RichardKroesen/M33-Sound-Locator/analysis/insights/24125-geometric_accuracy_plot.png

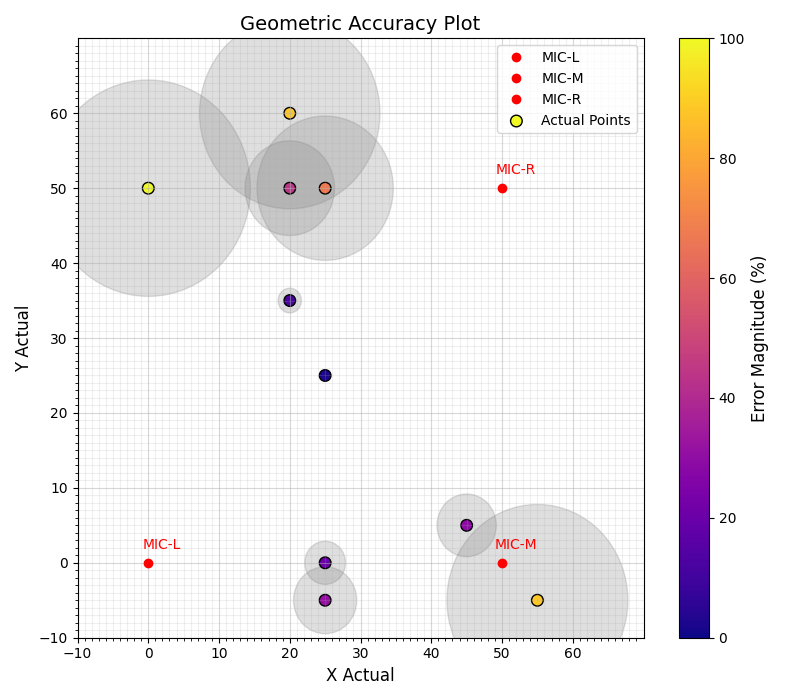
analysis/insights/24125-geometric_accuracy_plot.png
