RichardKroesen/M33-Sound-Locator/analysis/insights/AfterHW-LPF.png

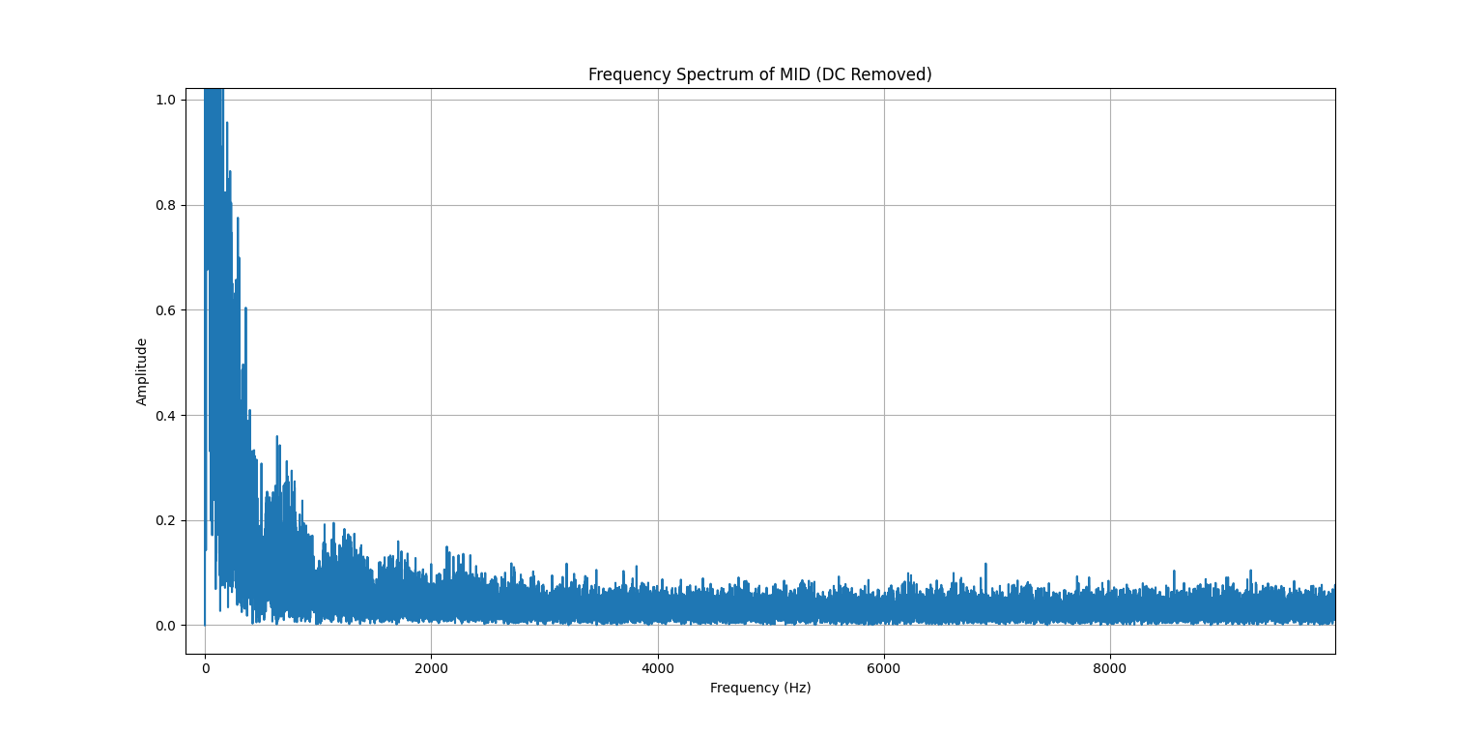
analysis/insights/AfterHW-LPF.png
