RichardKroesen/M33-Sound-Locator/analysis/insights/SW_FIR_signal_optimal_fcent4k-BW5-tps51.png

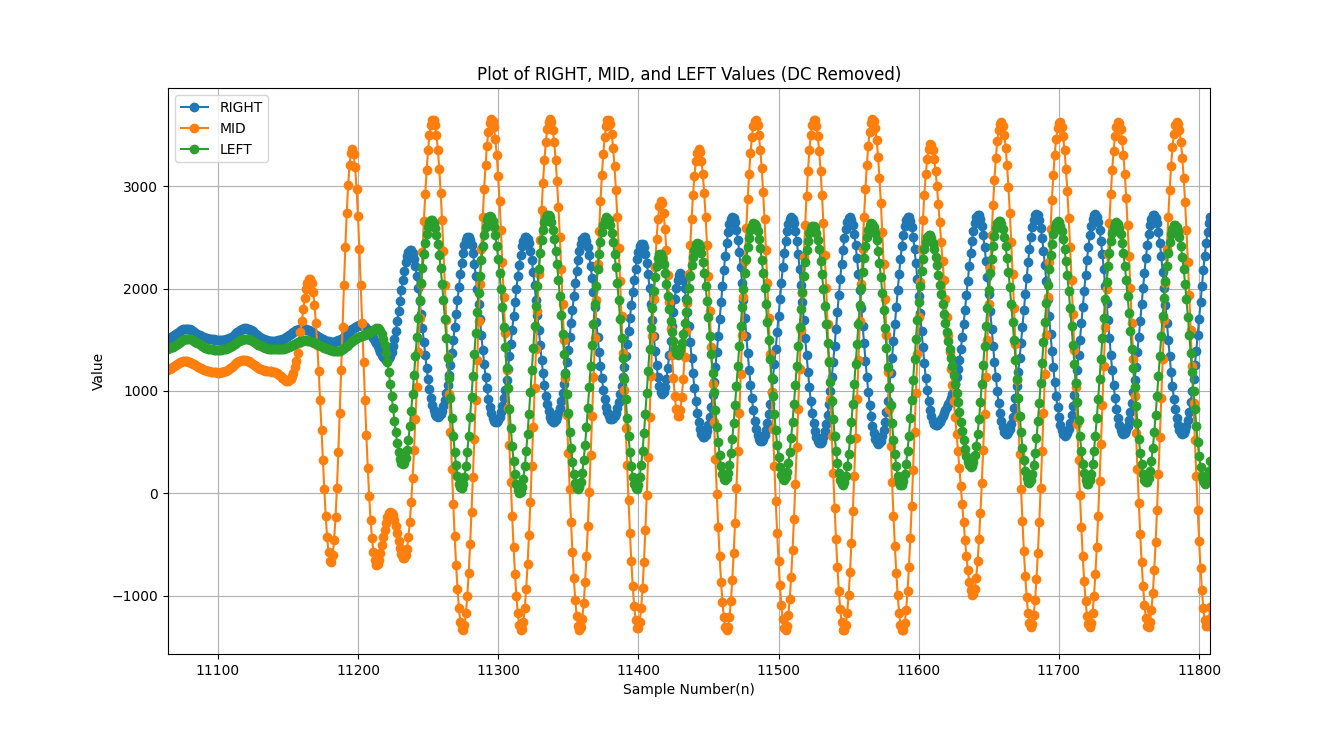
analysis/insights/SW_FIR_signal_optimal_fcent4k-BW5-tps51.png
