RichardKroesen/M33-Sound-Locator/electrical-mechnical-rsc/microphone-holder_sideview2.jpg

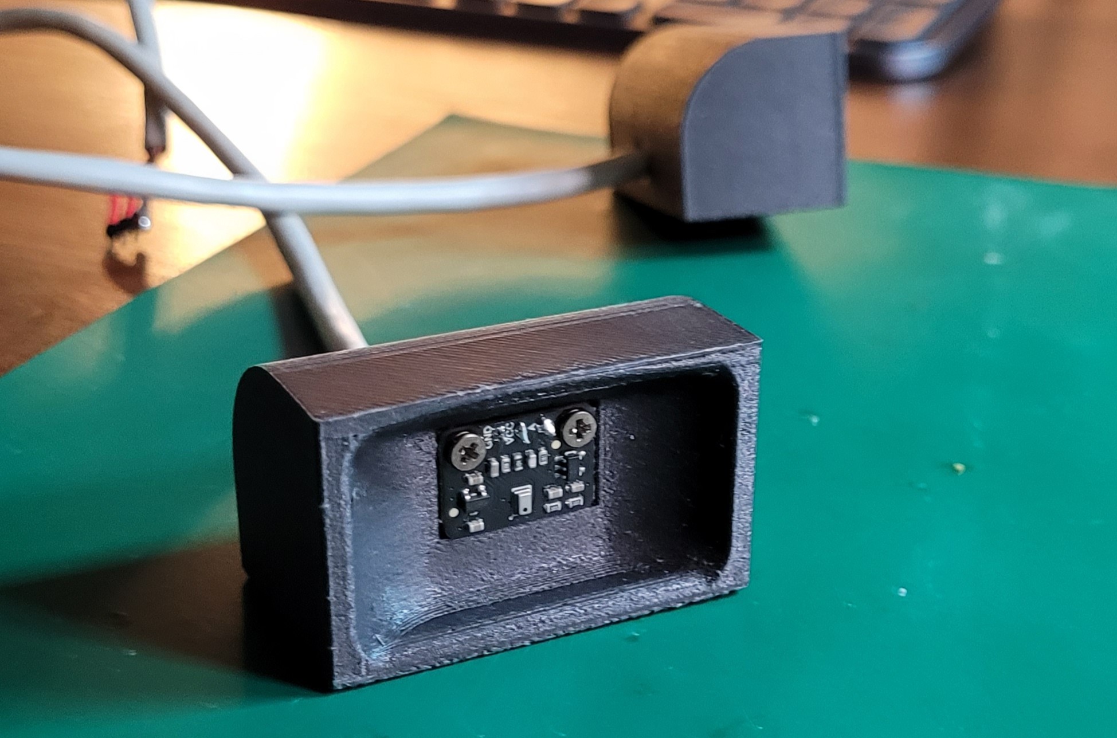
electrical-mechnical-rsc/microphone-holder_sideview2.jpg
