RichardKroesen/M33-Sound-Locator/electrical-mechnical-rsc/microphone_amplifier/perf-board_bottomview.jpg

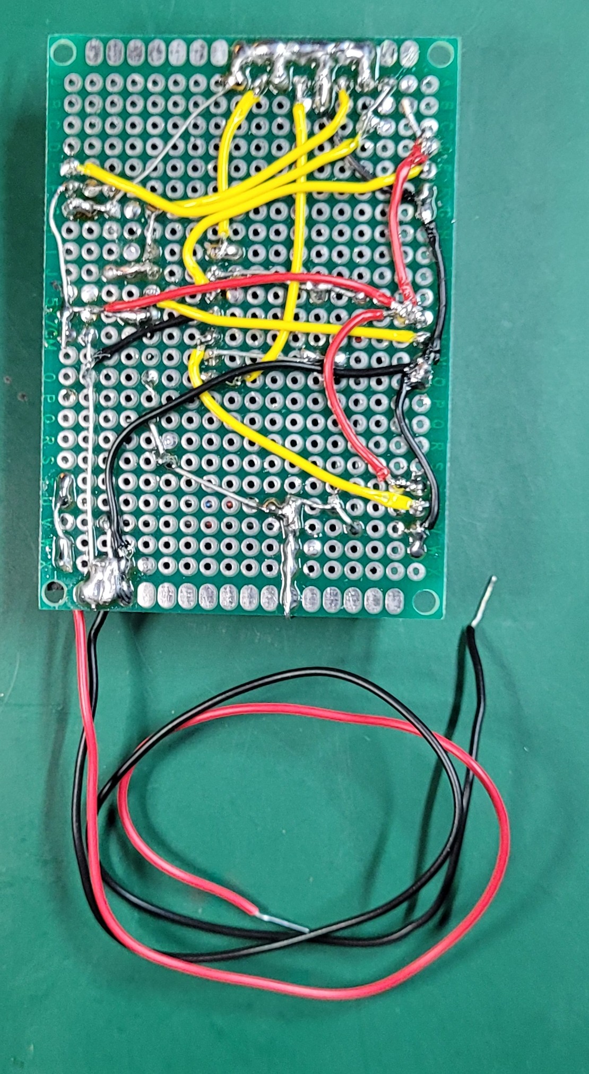
electrical-mechnical-rsc/microphone_amplifier/perf-board_bottomview.jpg
