RichardKroesen/M33-Sound-Locator/electrical-mechnical-rsc/microphone_amplifier/perf-board_topview.jpg

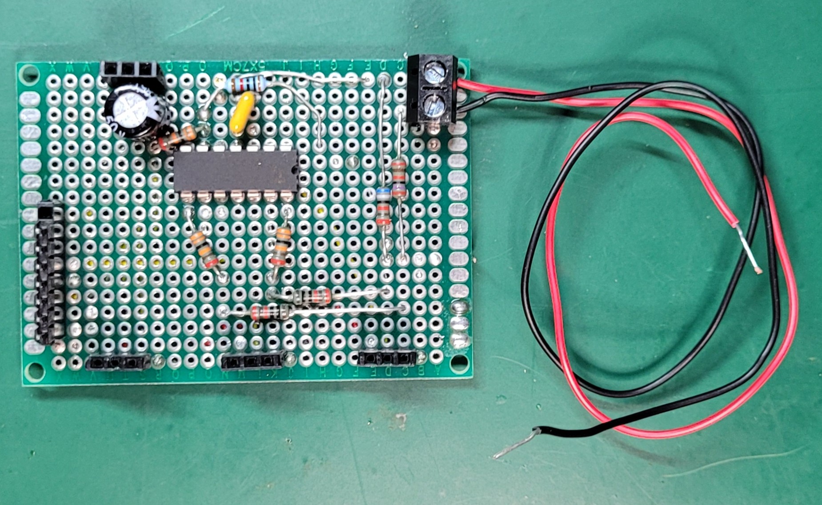
electrical-mechnical-rsc/microphone_amplifier/perf-board_topview.jpg
