RichardKroesen/M33-Sound-Locator/electrical-mechnical-rsc/Complete_hardware_setup_overview.jpg

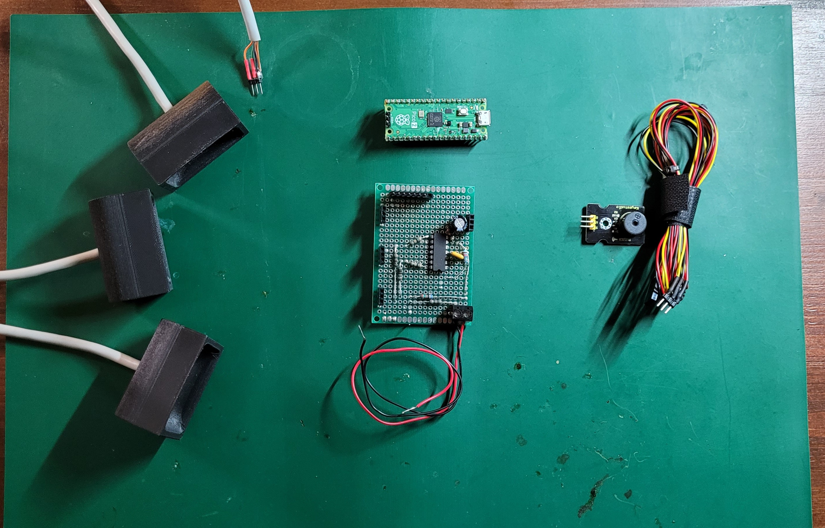
electrical-mechnical-rsc/Complete_hardware_setup_overview.jpg
