RichardKroesen/M33-Sound-Locator/models/Amplifier/AmplifierModel.asc

R1: res; 15k
R2: res; 200k
R3: res; 1
R4: res; 68k
R5: res; 27k
U1: LT1413
V1: voltage; 5
V2: voltage; SINE(1.5 0.15 1)
V3: voltage; 0
V4: voltage; 5
Named nets: 0, OutputSig
.tran 10
