RichardKroesen/M33-Sound-Locator/src/main.hpp

/** MIT License
 * 
 * Copyright (c) 2025 Feb. by Julian Bruin, James Schutte, Richard Kroesen
 * 
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
 * THE SOFTWARE IS PROVIDED "AS IS", WITHOUT WARRANTY OF ANY KIND, EXPRESS OR
 * IMPLIED, INCLUDING BUT NOT LIMITED TO THE WARRANTIES OF MERCHANTABILITY,
 * FITNESS FOR A PARTICULAR PURPOSE AND NONINFRINGEMENT. IN NO EVENT SHALL THE
 * AUTHORS OR COPYRIGHT HOLDERS BE LIABLE FOR ANY CLAIM, DAMAGES OR OTHER
 * LIABILITY, WHETHER IN AN ACTION OF CONTRACT, TORT OR OTHERWISE, ARISING FROM,
 * OUT OF OR IN CONNECTION WITH THE SOFTWARE OR THE USE OR OTHER DEALINGS IN THE
 * SOFTWARE.
 */

/* Standard libraries: */
#include <cstdio>

/* External Libraries */
#include "FreeRTOS.h"
#include "task.h"
#include "pico/stdlib.h"
#include "arm_math.h"

/* Codebase Includes */
#include "board_defines.h"
#include "adc_driver_dma.hpp"
#include "adc_sample_distributor.hpp"
#include "microphone_sensor.hpp"
#include "locator.hpp"
#include "SampleProcessor.h"
#include "buzzer.hpp"
#include "button_detector.hpp"

/* Listed Tasks */
void heart_beat_task(void *params) {
    gpio_init(PICO_DEFAULT_LED_PIN);
    gpio_set_dir(PICO_DEFAULT_LED_PIN, GPIO_OUT);

	printf("HeartBeat_start\n");

	for (;;) {
        gpio_put(PICO_DEFAULT_LED_PIN, 1);
		vTaskDelay(3000);
        printf("Heartbeat...\n");
        gpio_put(PICO_DEFAULT_LED_PIN, 0);
        vTaskDelay(3000);
	}
}

void mics_sample_log_task(void *param) {
    // Defines
    constexpr uint32_t post_processing_buffer_size = 1000;
    constexpr ADC_FREQUENCIES FS = ADC_FREQUENCIES::FS_MAX_PICO;
    constexpr uint32_t total_buffer_size = 60;
    constexpr uint32_t batch_buffer_size = 12;

    // Aliases
    using Microphone0 = SENSOR::Microphone<0, post_processing_buffer_size>;
    using Microphone1 = SENSOR::Microphone<1, post_processing_buffer_size>;
    using Microphone2 = SENSOR::Microphone<2, post_processing_buffer_size>;
    
    // Objects 
    auto mic0 = std::make_shared<Microphone0>();
    auto mic1 = std::make_shared<Microphone1>();
    auto mic2 = std::make_shared<Microphone2>();
    static ADC::SampleDistributor<ADC::ISensor, 3> distributor({mic0, mic1, mic2});
    static ADC::ADC_Driver_DMA<FS, total_buffer_size, batch_buffer_size> adc_driver;

    // Common buffer 
    static std::unique_ptr<uint16_t[]> buffer = std::make_unique<uint16_t[]>(batch_buffer_size);
    
    // ADC setup  
    adc_driver.set_notification_task(xTaskGetCurrentTaskHandle());
    adc_driver.start_adc();

    while (true) {
        // Blocked until there is a notification, from DMA ADC IRQ: 
        ulTaskNotifyTake(pdTRUE, portMAX_DELAY);

        // Buffer Processing: 
        adc_driver.copy_buffer(buffer, batch_buffer_size);
        for (uint32_t i = 0; i < batch_buffer_size-2; i = i + 3) {
            printf("%u,%u,%u\n", buffer[i], buffer[i+1], buffer[i+2]);
        }
        distributor.distribute_samples<batch_buffer_size>(buffer);

        adc_driver.start_adc(); /* At this moment ADC restarts after processing.
                                 * Since it is not yet known if processing is 
                                 * less than the ADC DMA timing */
    }
}

void trigger_buz_on_button_task(void *param) {
    // Defines
    constexpr uint8_t button_pin = UTILS::PinManager::GPIO::BUZ_ACTIVATE;
    constexpr uint8_t buz_pin = UTILS::PinManager::GPIO::BUZ_OUTPUT;
    constexpr uint32_t freq = 4000;
    constexpr uint16_t width = 150; 

    // Objects 
    static ACTUATOR::Buzzer<buz_pin> buz{};
    static SENSOR::ButtonDetector<button_pin> button{}; 

    // Setup 
    buz.set_tone_frequency(freq);
    button.set_notification_task(xTaskGetCurrentTaskHandle());
    button.enable_detection();

    while (true) {
        ulTaskNotifyTake(pdTRUE, portMAX_DELAY);
        buz.start_buzzer(width);
    }
}
